Bastelkwast/GPS-OILER-2/Bild_2.png

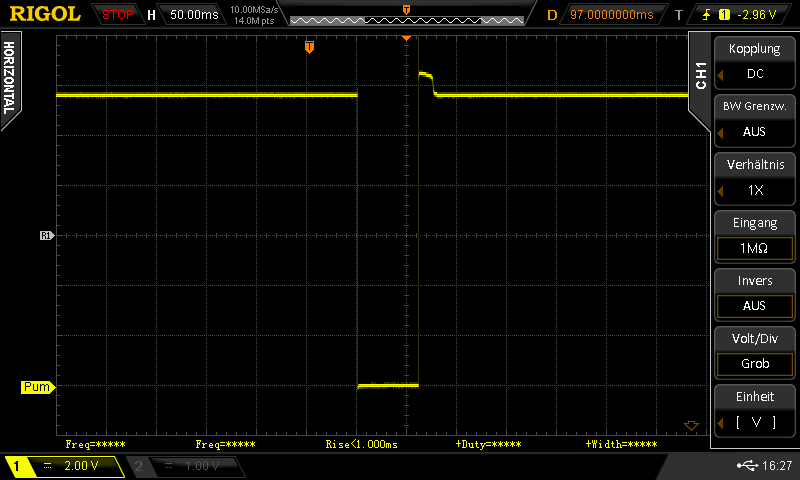
Bild_2.png
