Bastelkwast/GPS-OILER-2/docs/Tracer_900GT/PNG/Gehäuse_innen.png

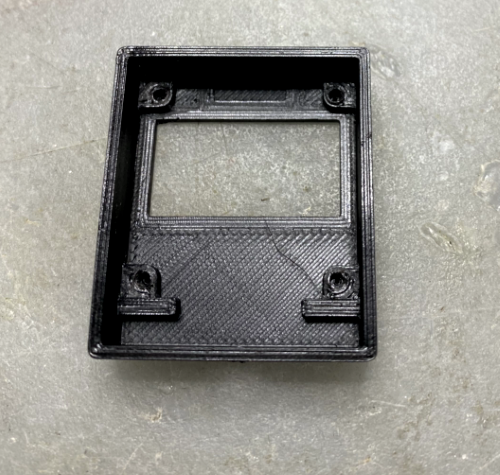
docs/Tracer_900GT/PNG/Gehäuse_innen.png
