Bastelkwast/GPS-OILER-2/docs/Tracer_900GT/PNG/IMG_1259.png

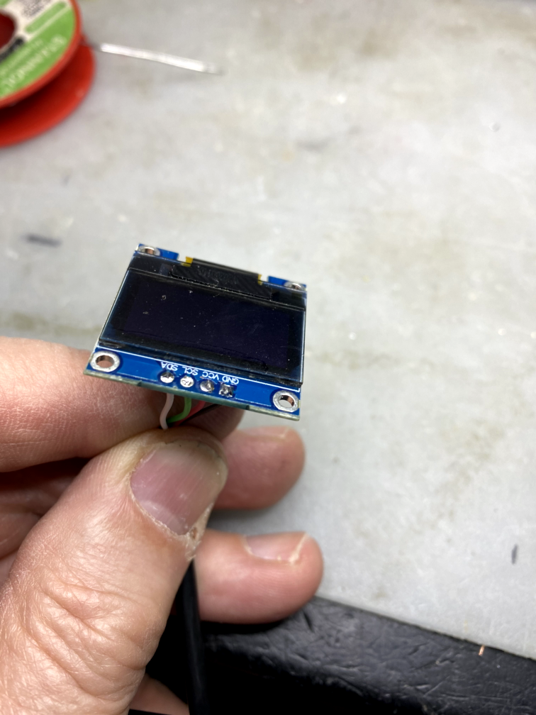
docs/Tracer_900GT/PNG/IMG_1259.png
