Bastelkwast/GPS-OILER-2/docs/Tracer_900GT/PNG/OLED_1.png

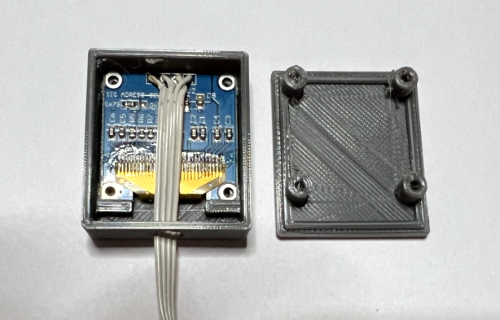
docs/Tracer_900GT/PNG/OLED_1.png
