Bastelkwast/GPS-OILER-2/DS2_20230807184204.png

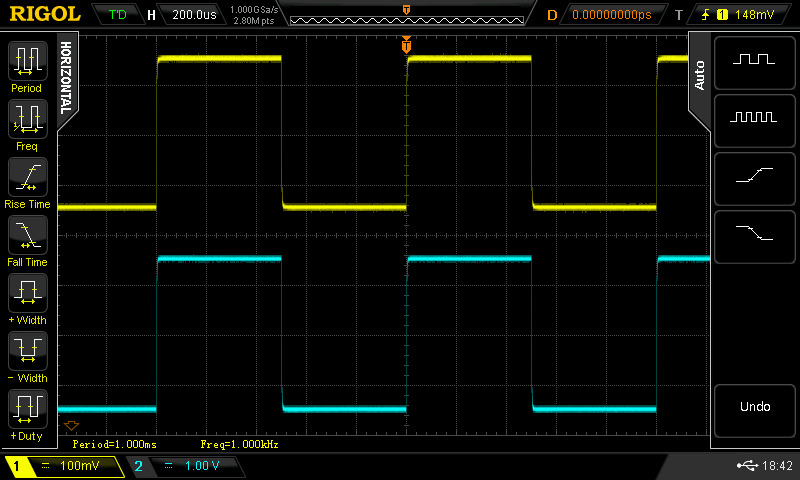
DS2_20230807184204.png
