Bastelkwast/GPS-OILER-2/DS2_20230807184304.png

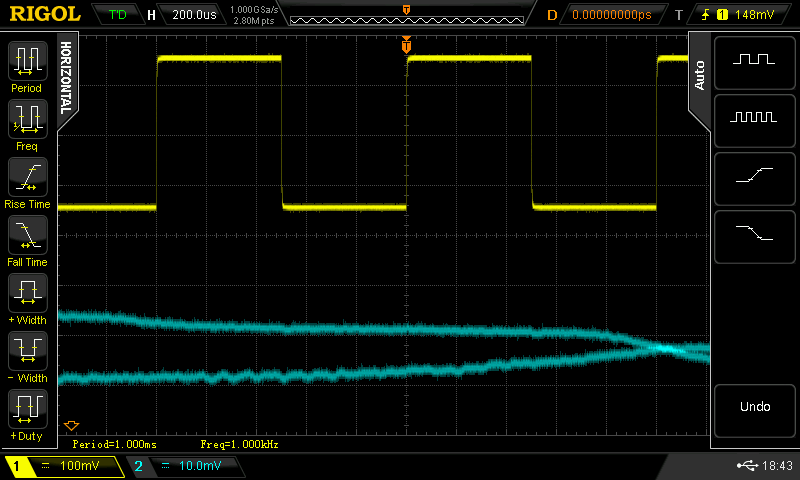
DS2_20230807184304.png
