Bastelkwast/GPS-OILER-2/DS2_20230811154746.png

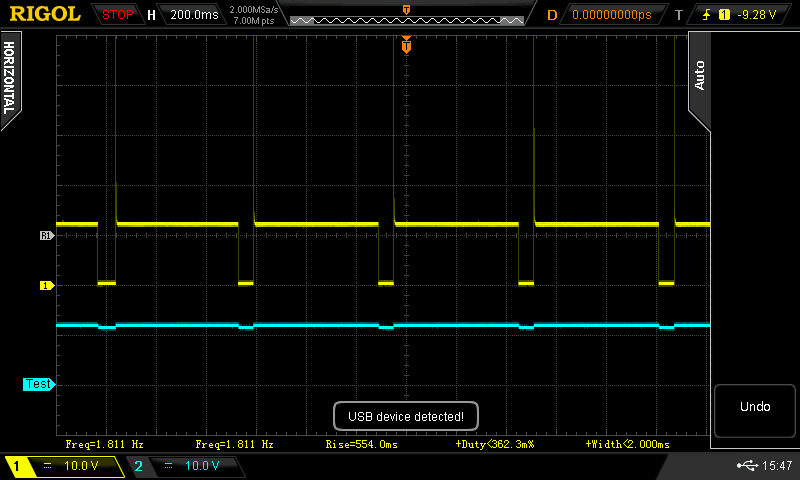
DS2_20230811154746.png
