Bastelkwast/GPS-OILER-2/DS2_20230811154827.png

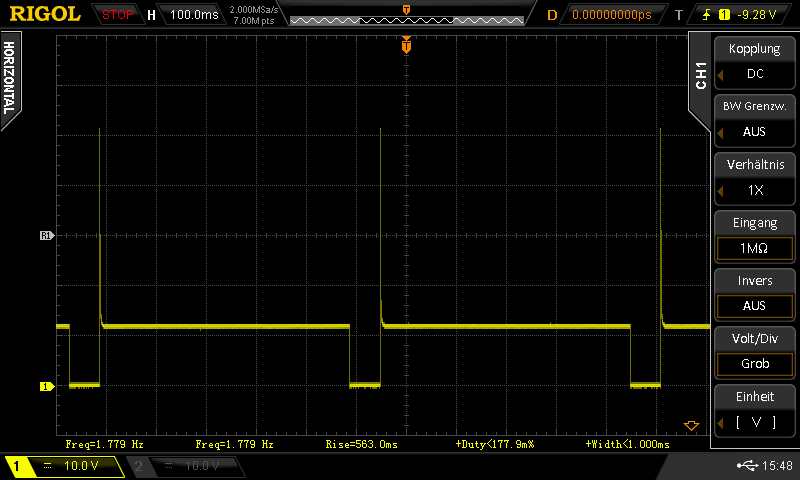
DS2_20230811154827.png
