Bastelkwast/GPS-OILER-2/DS2_20230811155615.png

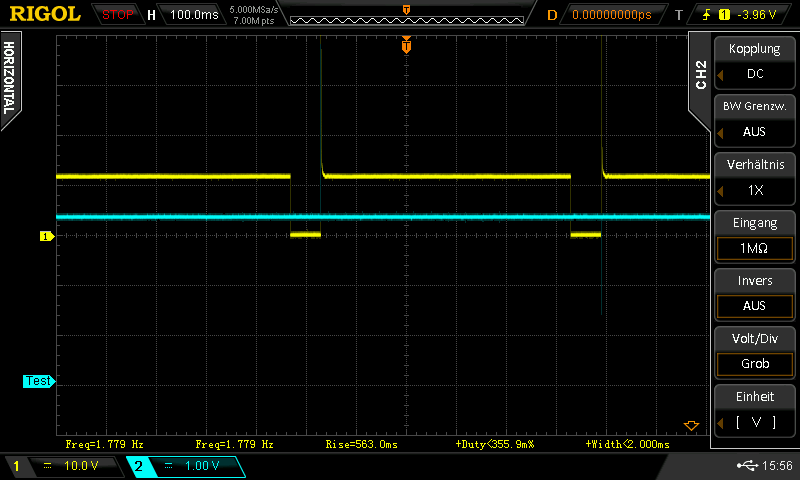
DS2_20230811155615.png
